KevinPlt/DIY-stabilized-power-supply/DXF/left_side.DXF

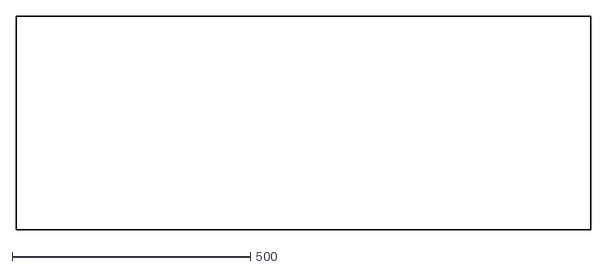
[picture p19: CAD file, 2022-04-26]
DXF/left_side.DXF
1205.7 x 447.6
