KevinPlt/DIY-stabilized-power-supply/Solidworks_Sources/DPX_UART.SLDPRT

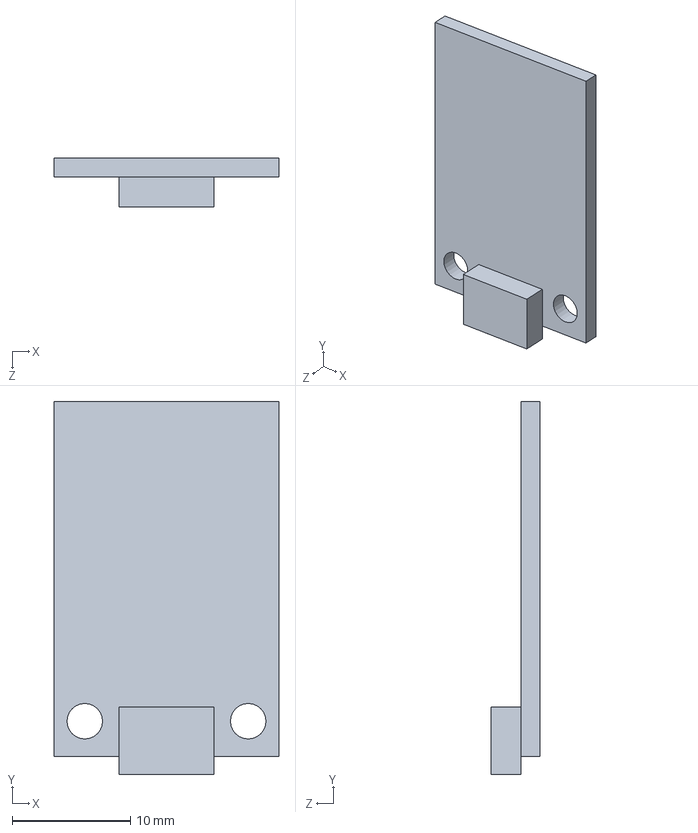
[picture p20: CAD file, 2022-04-26]
Solidworks_Sources/DPX_UART.SLDPRT
19.0 x 31.5 x 4.10 mm
