KevinPlt/DIY-stabilized-power-supply/Solidworks_Sources/ATXPowerSupply.SLDPRT

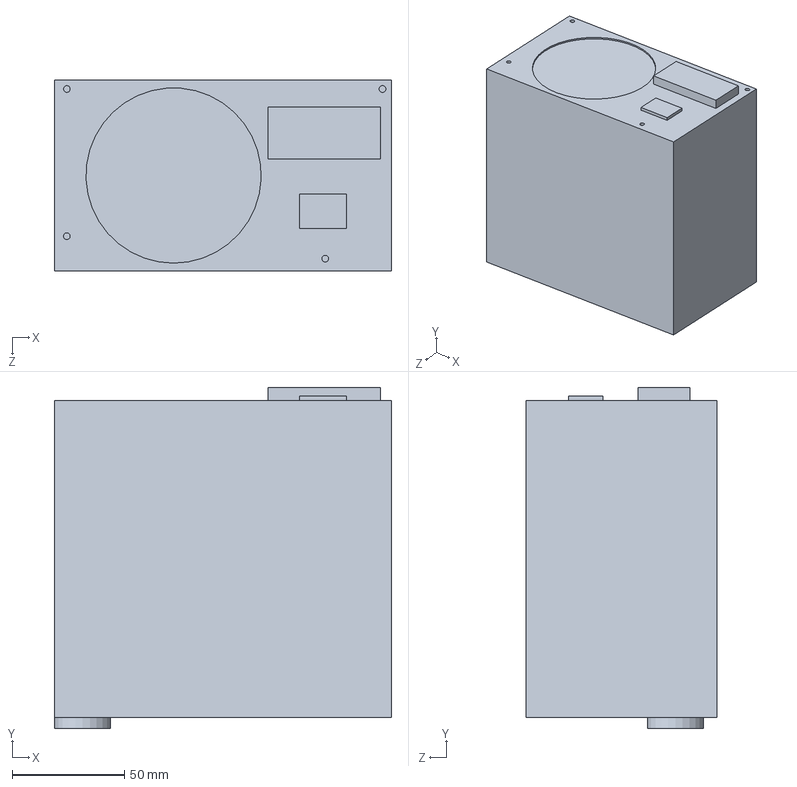
[picture p21: CAD file, 2022-04-26]
Solidworks_Sources/ATXPowerSupply.SLDPRT
150.0 x 152.0 x 85.0 mm
