KevinPlt/DIY-stabilized-power-supply/Solidworks_Sources/bottom_side.SLDPRT

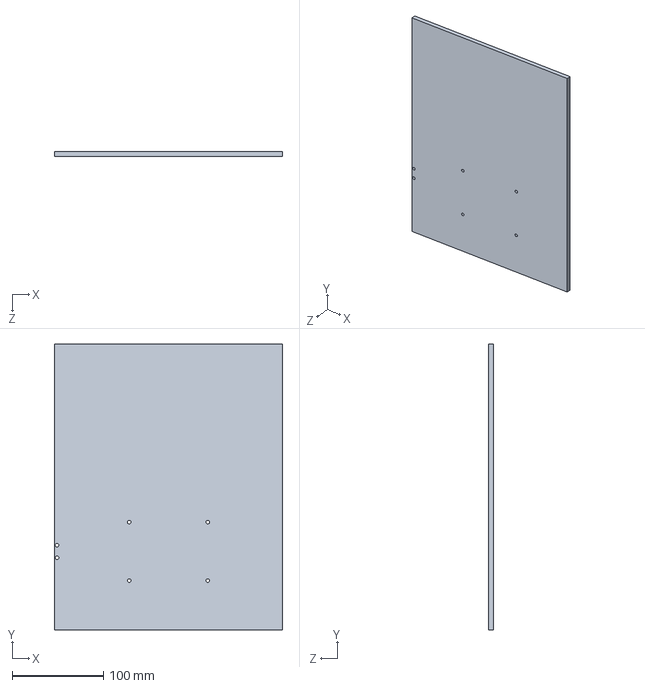
[picture p22: CAD file, 2022-04-26]
Solidworks_Sources/bottom_side.SLDPRT
250.0 x 313.0 x 6.00 mm
