KevinPlt/DIY-stabilized-power-supply/Solidworks_Sources/front_side.SLDPRT

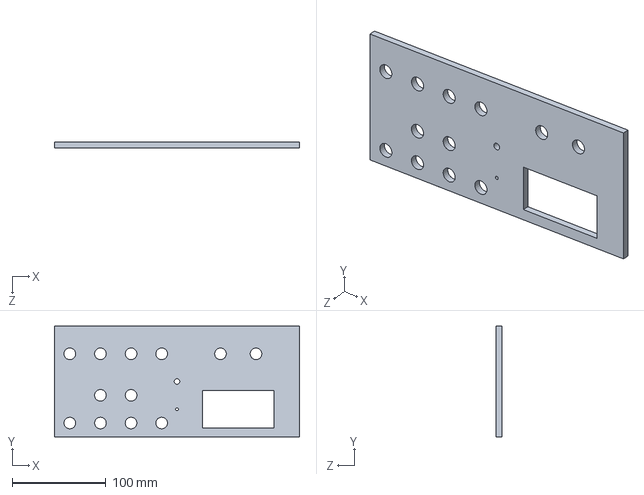
[picture p23: CAD file, 2022-04-26]
Solidworks_Sources/front_side.SLDPRT
262.0 x 118.4 x 6.00 mm
