KevinPlt/DIY-stabilized-power-supply/Solidworks_Sources/DPHScreen.SLDPRT

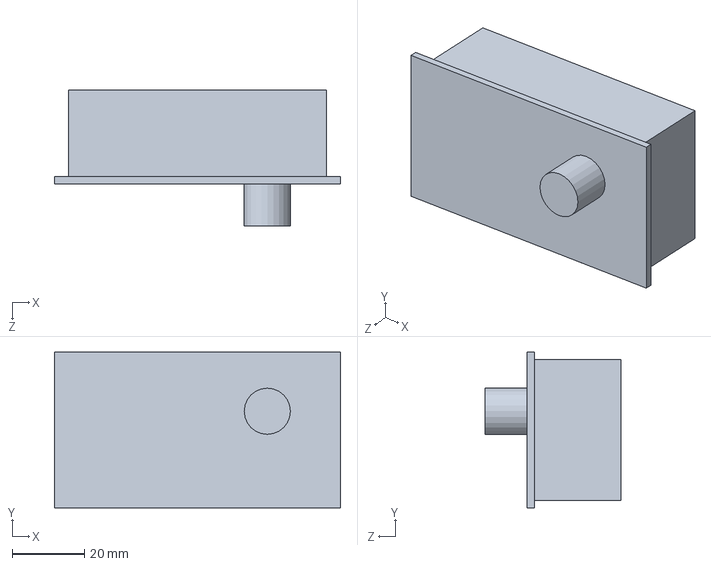
[picture p24: CAD file, 2022-04-26]
Solidworks_Sources/DPHScreen.SLDPRT
79.3 x 43.2 x 37.7 mm
