KevinPlt/DIY-stabilized-power-supply/Solidworks_Sources/top_side.SLDPRT

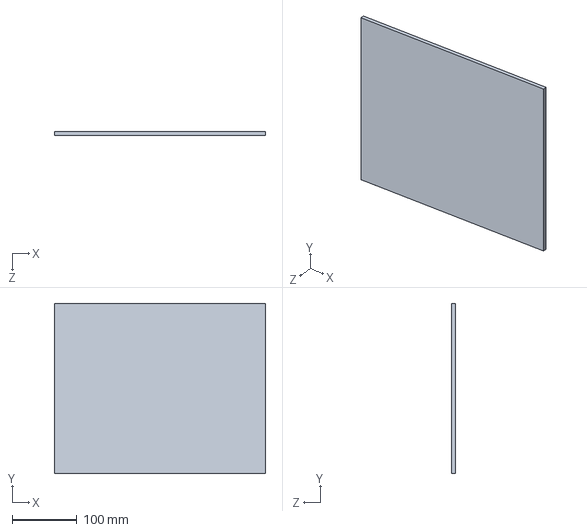
[picture p25: CAD file, 2022-04-26]
Solidworks_Sources/top_side.SLDPRT
325.0 x 262.0 x 6.00 mm
